xventus/Church-psalm-hymn-display/controller/DOC/images/IMG_4634.jpg

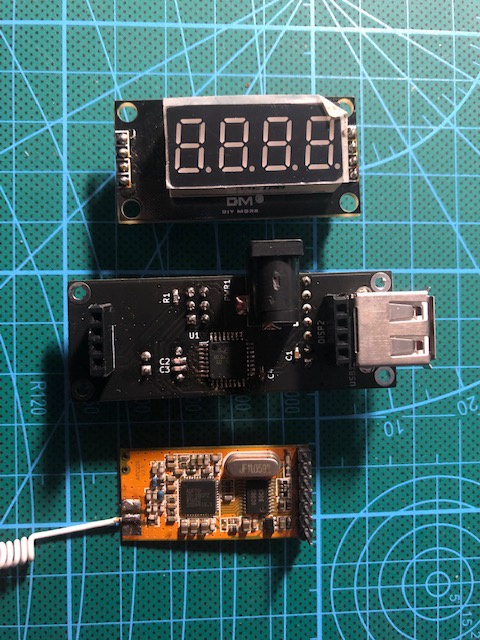
controller/DOC/images/IMG_4634.jpg
