xventus/Church-psalm-hymn-display/controller/DOC/images/IMG_4637.jpg

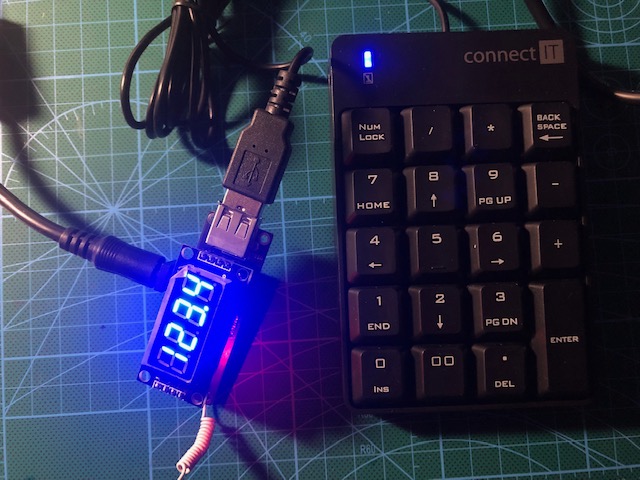
controller/DOC/images/IMG_4637.jpg
