xventus/Church-psalm-hymn-display/controller/DOC/images/IMG_4638.jpg

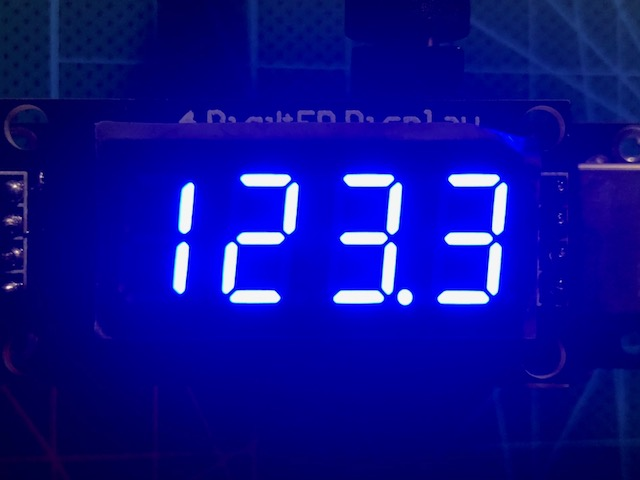
controller/DOC/images/IMG_4638.jpg
