xventus/Church-psalm-hymn-display/display/images/IMG_4640.jpg

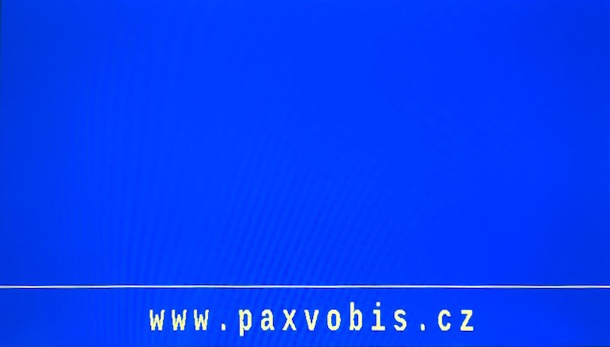
display/images/IMG_4640.jpg
