xventus/Church-psalm-hymn-display/display/images/IMG_4643.jpg

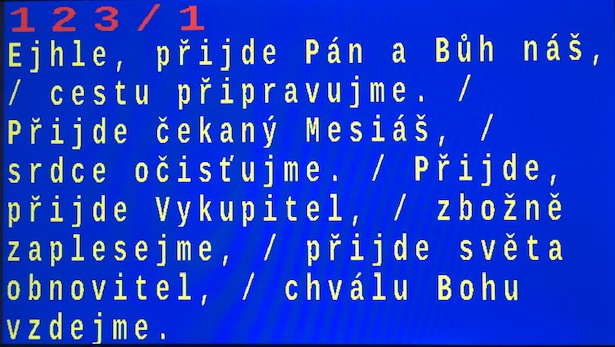
display/images/IMG_4643.jpg
