xventus/Church-psalm-hymn-display/display/images/IMG_4644.jpg

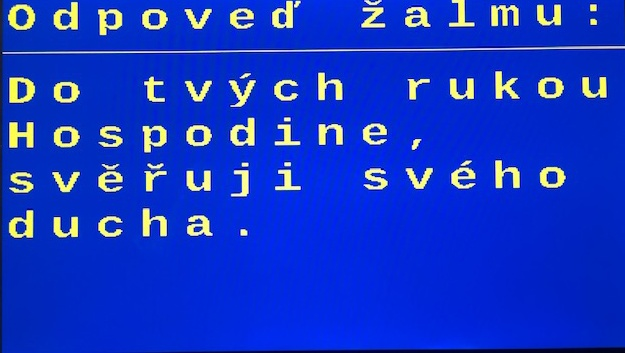
display/images/IMG_4644.jpg
